oliverhanka/eps32_cloud_pcb/ressources/PCB_Antenna_Lib/Datasheets/AN91445A.png

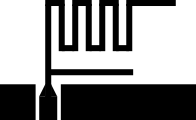
ressources/PCB_Antenna_Lib/Datasheets/AN91445A.png
