oliverhanka/eps32_cloud_pcb/ressources/PCB_Antenna_Lib/Datasheets/SWRA118.png

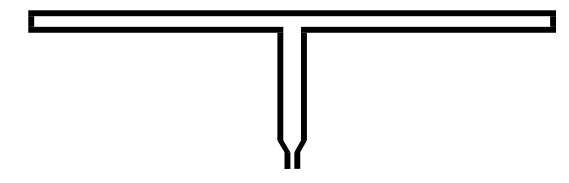
ressources/PCB_Antenna_Lib/Datasheets/SWRA118.png
