oliverhanka/eps32_cloud_pcb/ressources/PCB_Antenna_Lib/Datasheets/SWRA350A.png

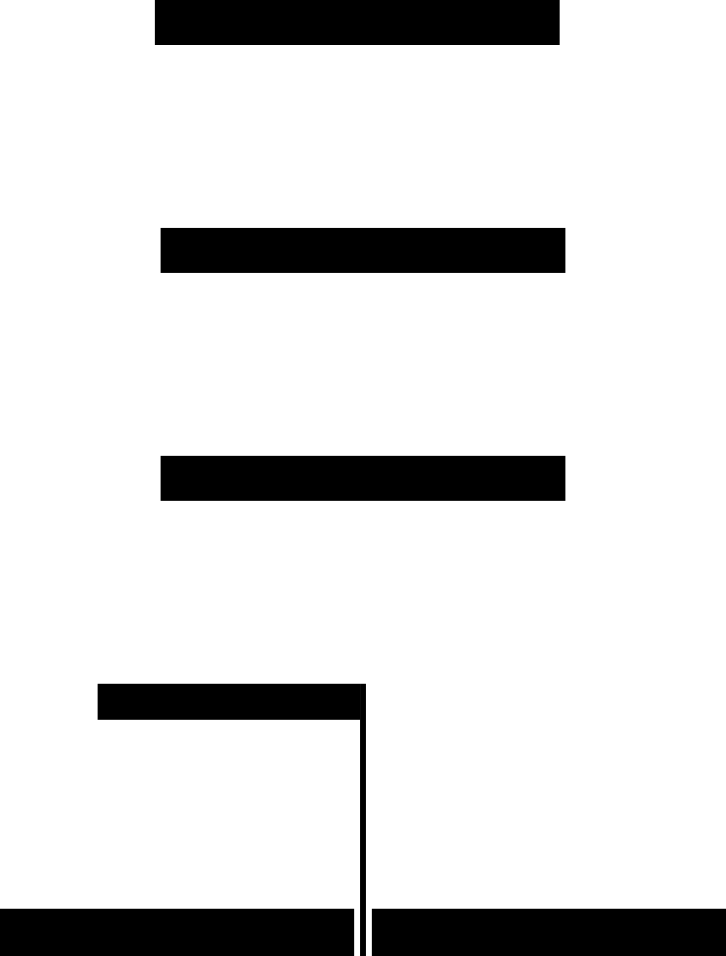
ressources/PCB_Antenna_Lib/Datasheets/SWRA350A.png
