oliverhanka/eps32_cloud_pcb/ressources/PCB_Antenna_Lib/Datasheets/SWRA350B.png

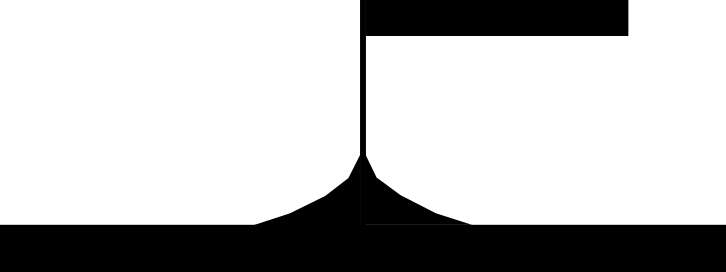
ressources/PCB_Antenna_Lib/Datasheets/SWRA350B.png
