oliverhanka/eps32_cloud_pcb/ressources/PCB_Antenna_Lib/Datasheets/swra416A.png

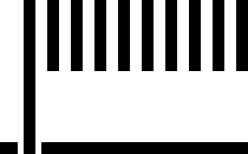
ressources/PCB_Antenna_Lib/Datasheets/swra416A.png
