oliverhanka/eps32_cloud_pcb/ressources/PCB_Antenna_Lib/JPGs/AN91445.jpg

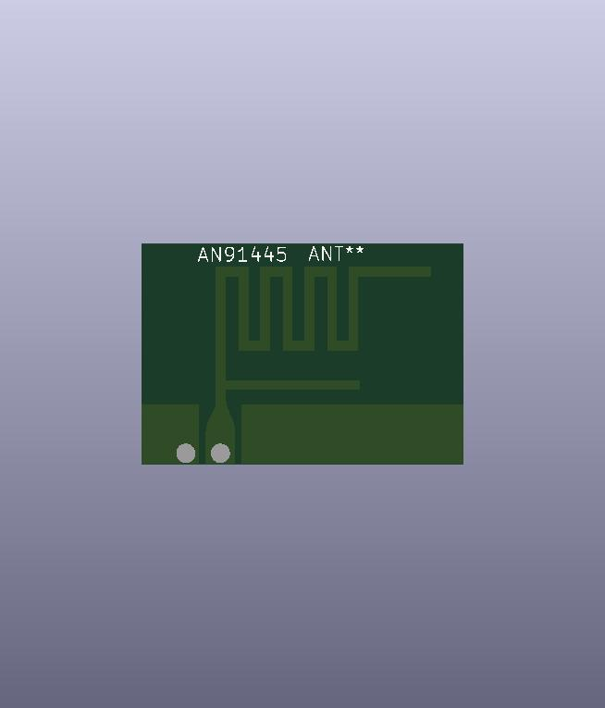
ressources/PCB_Antenna_Lib/JPGs/AN91445.jpg
