oliverhanka/eps32_cloud_pcb/ressources/PCB_Antenna_Lib/JPGs/SWRA117D.jpg

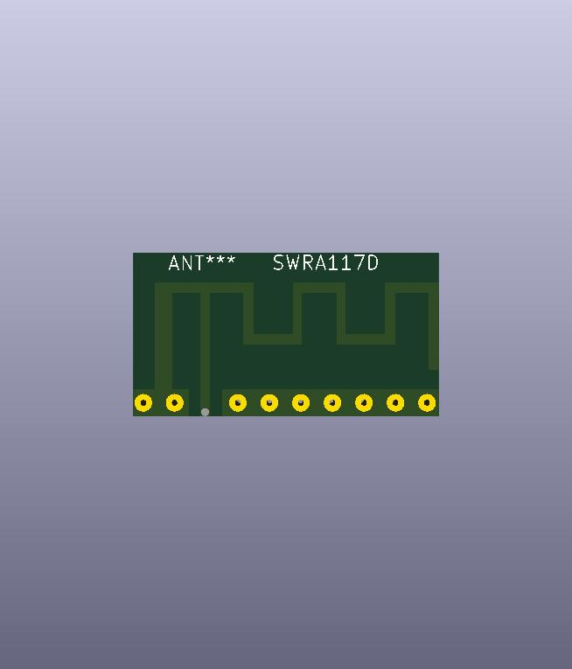
ressources/PCB_Antenna_Lib/JPGs/SWRA117D.jpg
