oliverhanka/eps32_cloud_pcb/ressources/PCB_Antenna_Lib/JPGs/SWRA416.jpg

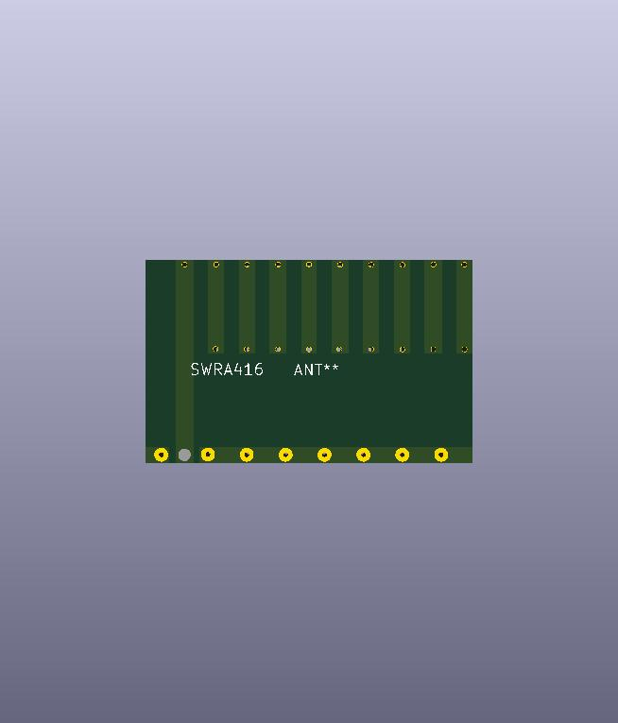
ressources/PCB_Antenna_Lib/JPGs/SWRA416.jpg
